gbulmer/openstm32hw/Orone-mini-v0/Orone-mini-S8J-v0r001/Orone-mini-S8J-v0r001.top.pdf

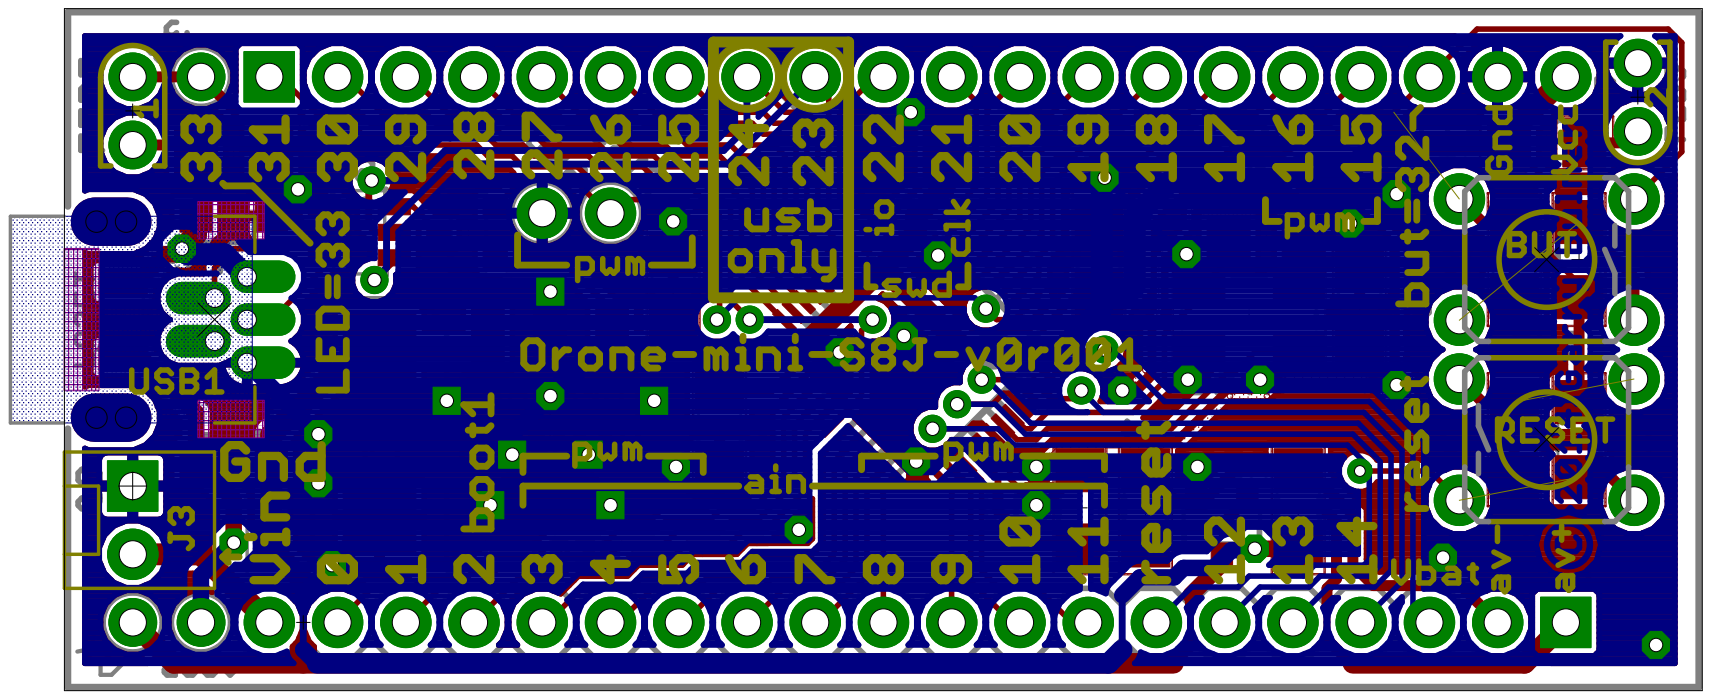
[picture p17: page 1]
