gbulmer/openstm32hw/Orone-mini-v0/Orone-mini-S8E-v0r001/Orone-mini-S8E-v0r001.pdf

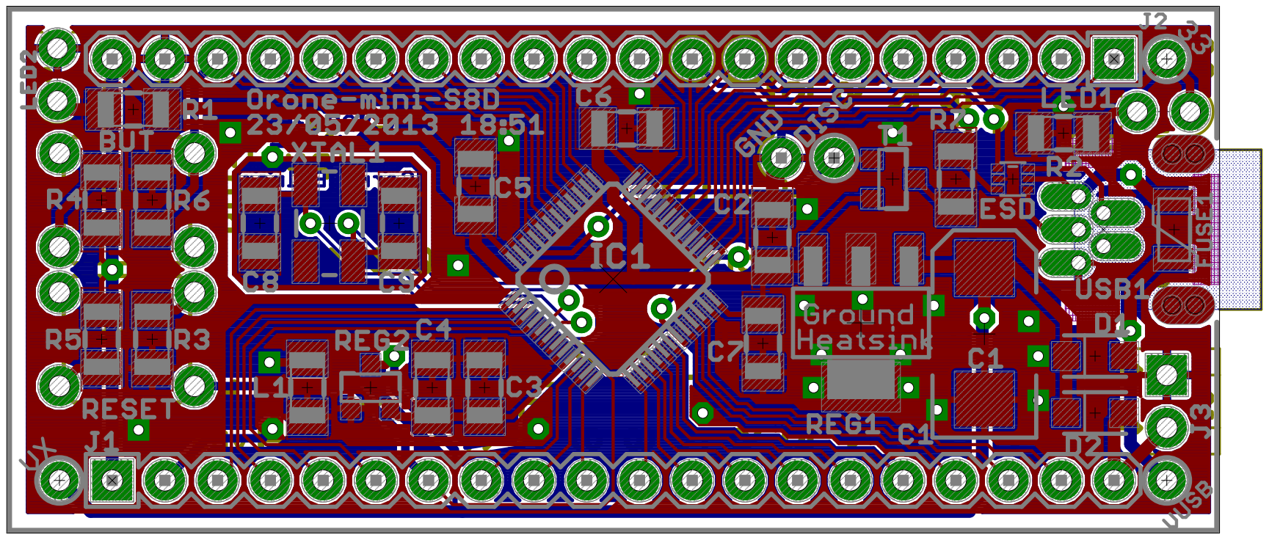
[picture p18: page 1]
