gbulmer/openstm32hw/Orone-mini-v0/Orone-mini-S8H-v0r001/Orone-mini-S8H-v0r001.pdf

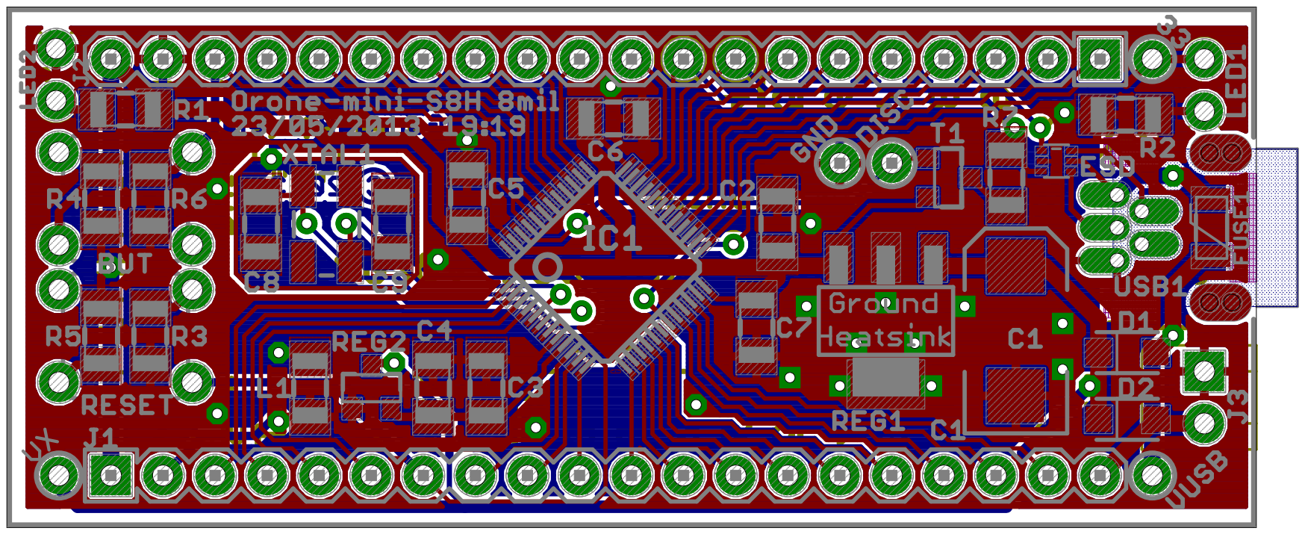
[picture p20: page 1]
