gbulmer/openstm32hw/Orone-mini-v0/Orone-mini-S8H-v0r001/Orone-mini-S8H-v0r001.top.pdf

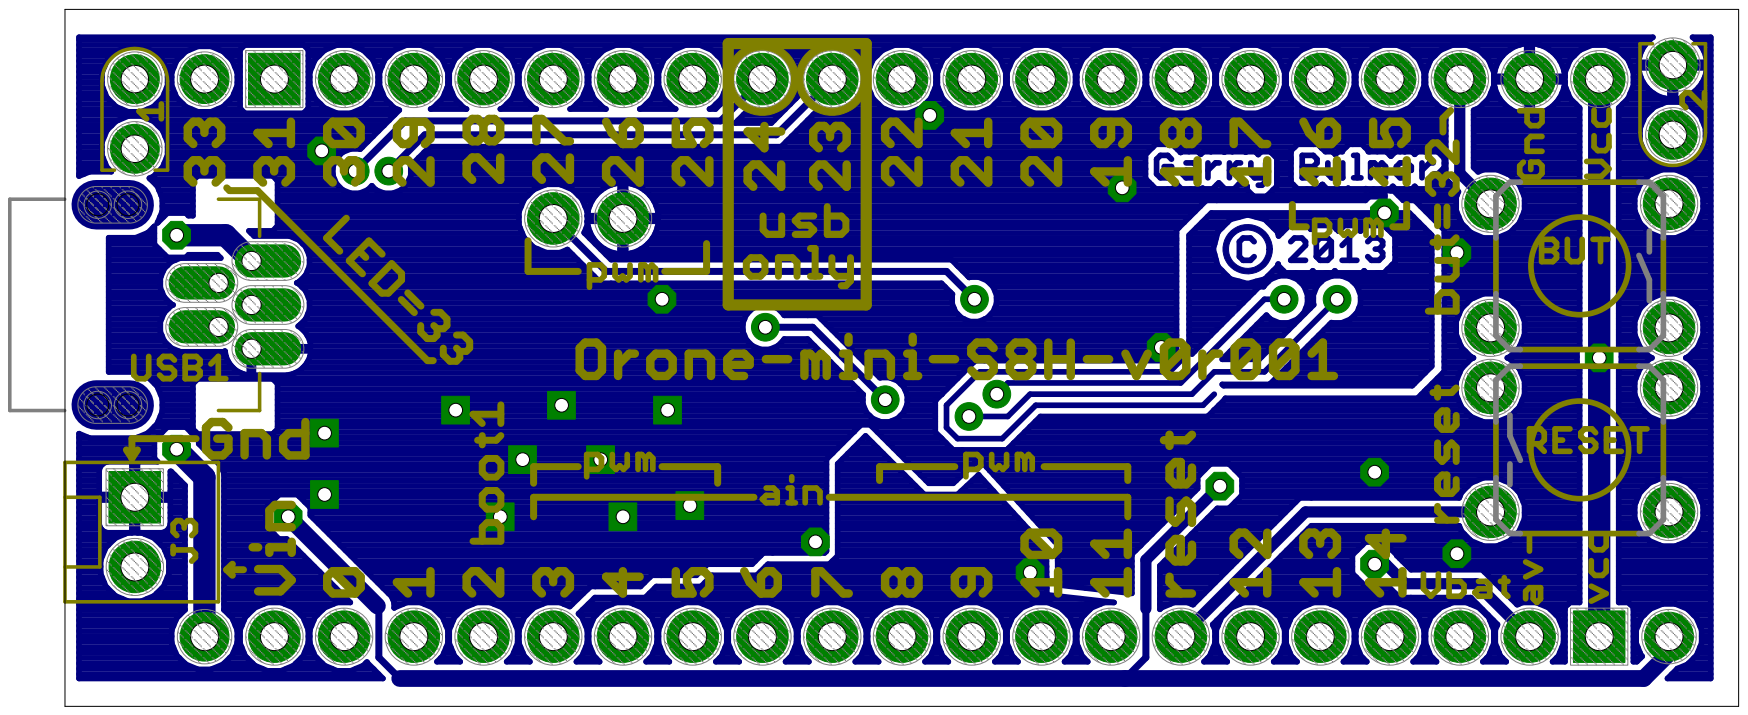
[picture p21: page 1]
