gbulmer/openstm32hw/Orone-mini-v0/Orone-mini-S8D-v0r001/Orone-mini-S8D-v0r001.sch.pdf

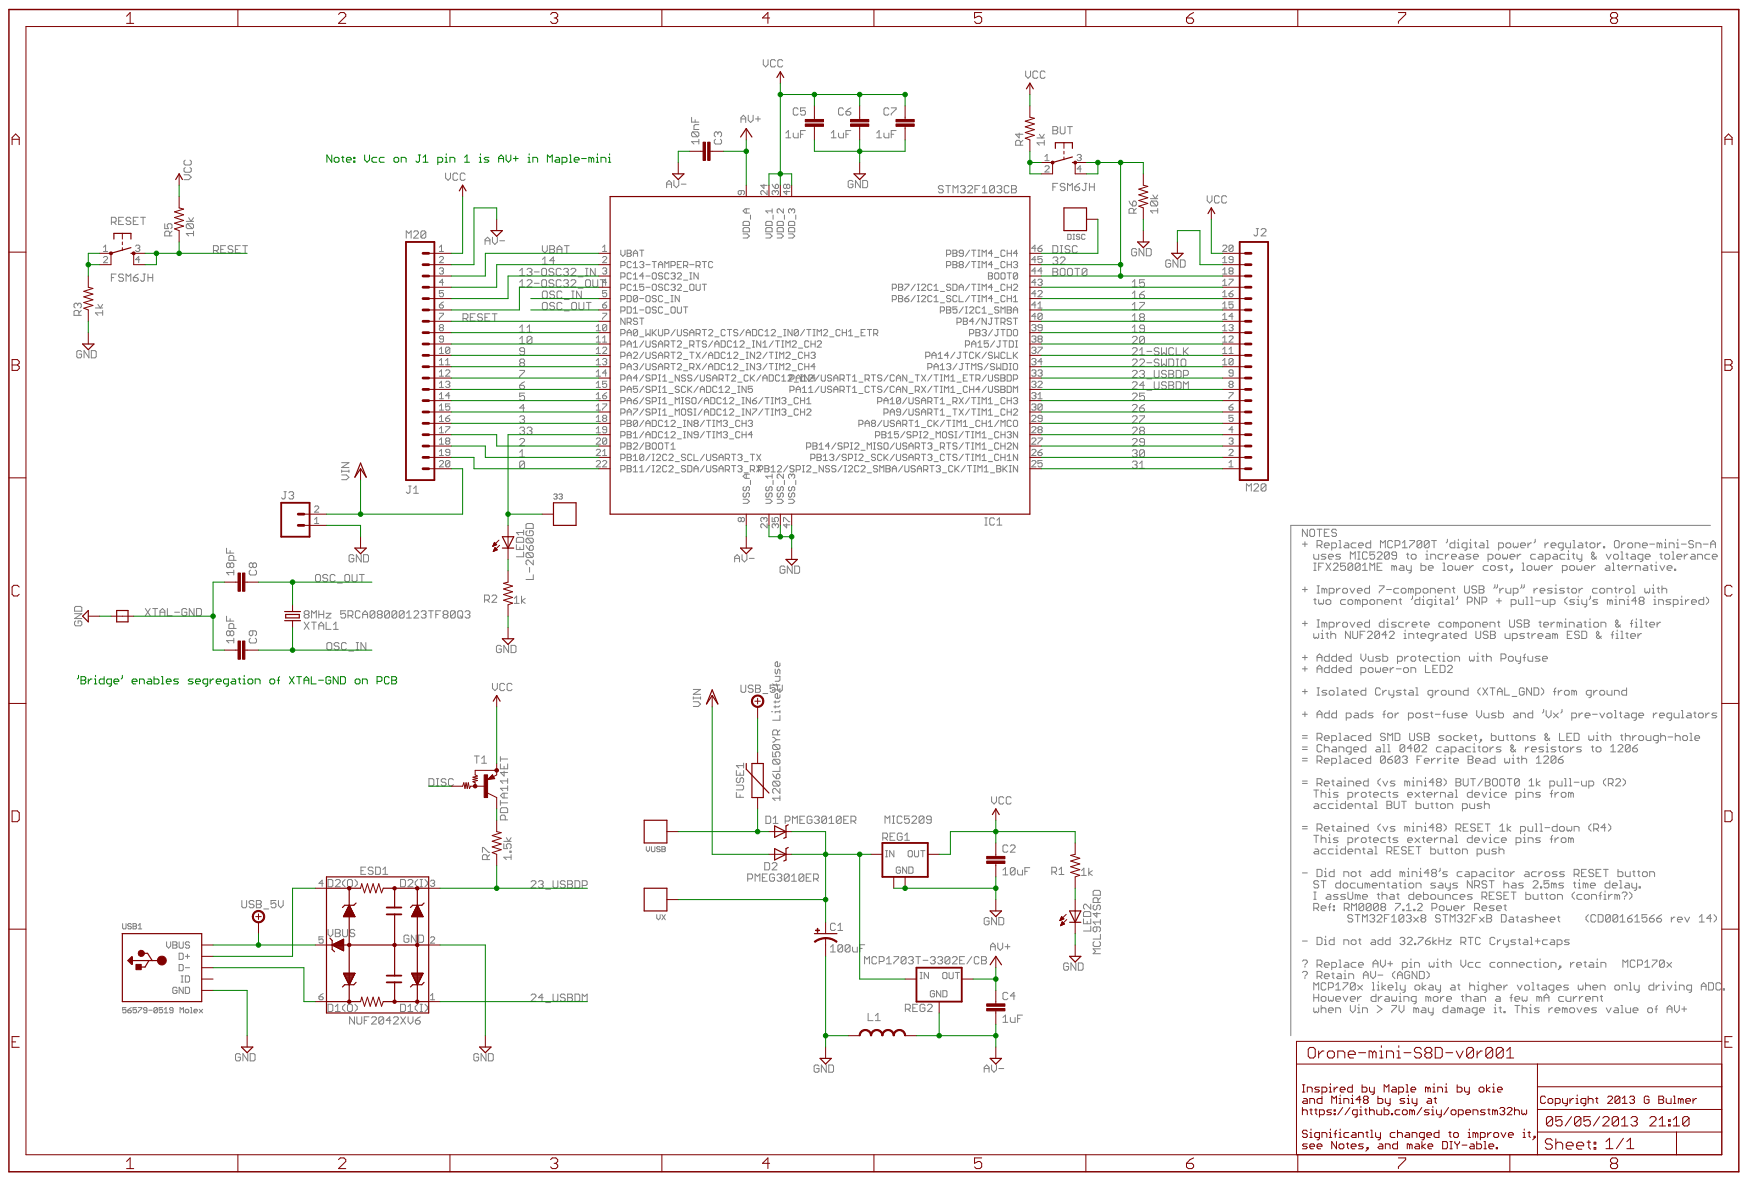
[picture p22: page 1]
