gbulmer/openstm32hw/Orone-mini-v0/Orone-mini-S8D-v0r001/Orone-mini-S8D-v0r001.pdf

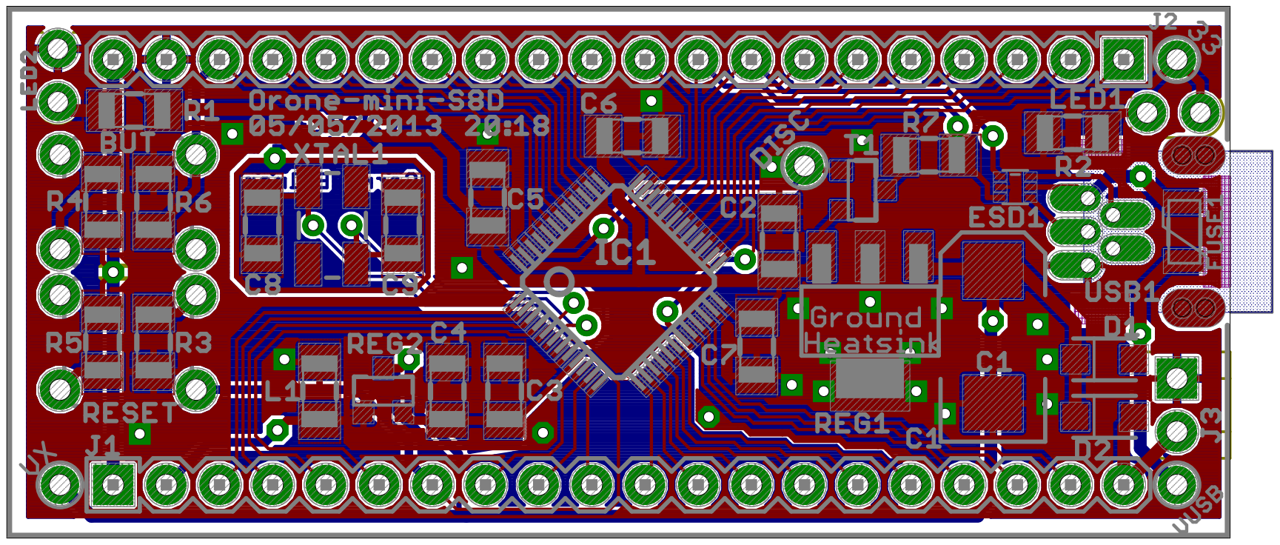
[picture p23: page 1]
