gbulmer/openstm32hw/Orone-mini-v0/Orone-mini-S8D-v0r001/Orone-mini-S8D-v0r001.top.pdf

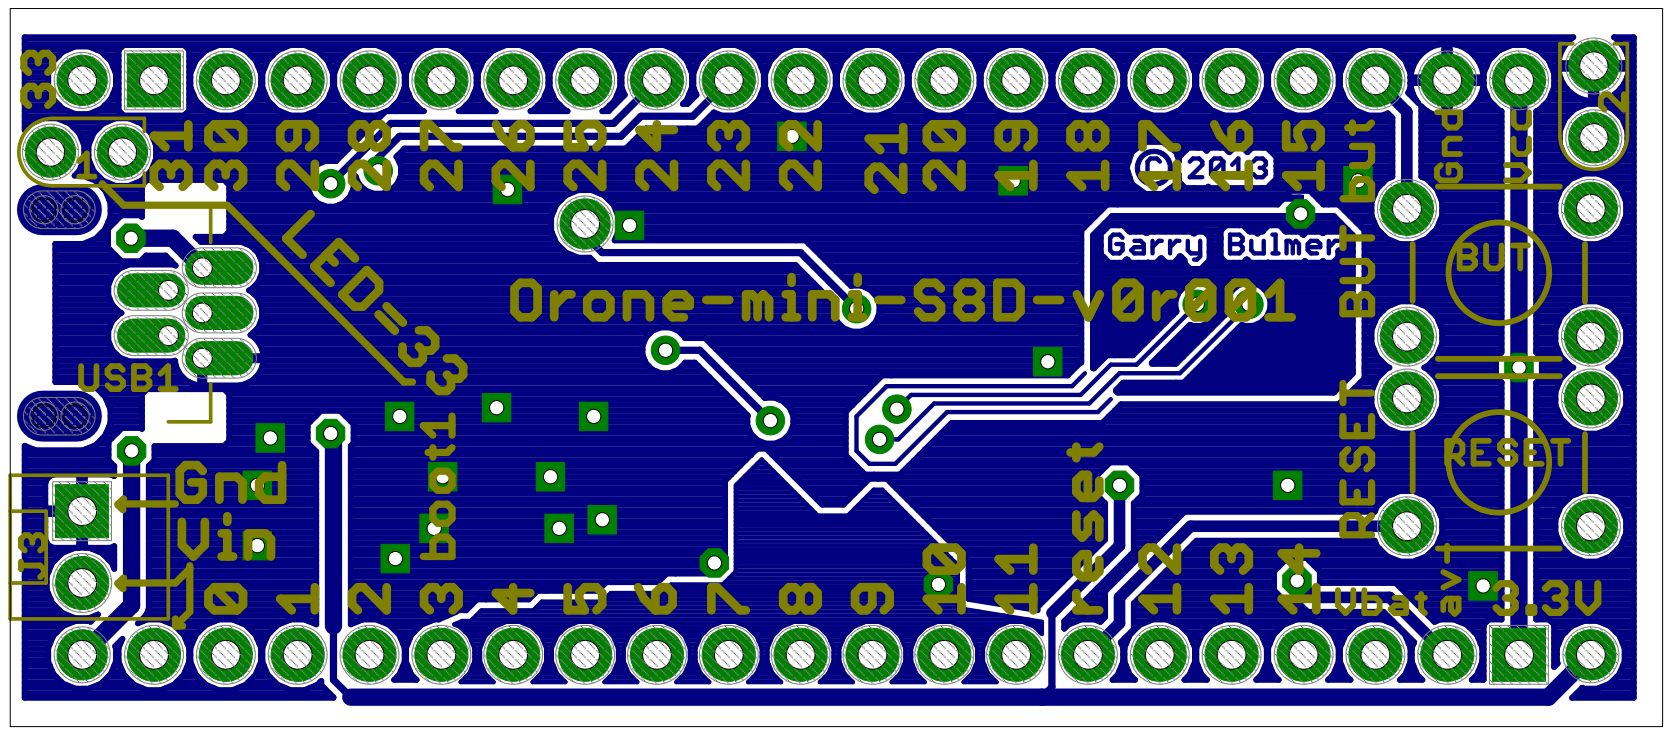
[picture p24: page 1]
