gbulmer/openstm32hw/Orone-mini-v0/Orone-mini-S8C-v0r001/Orone-mini-S8C-v0r001.pdf

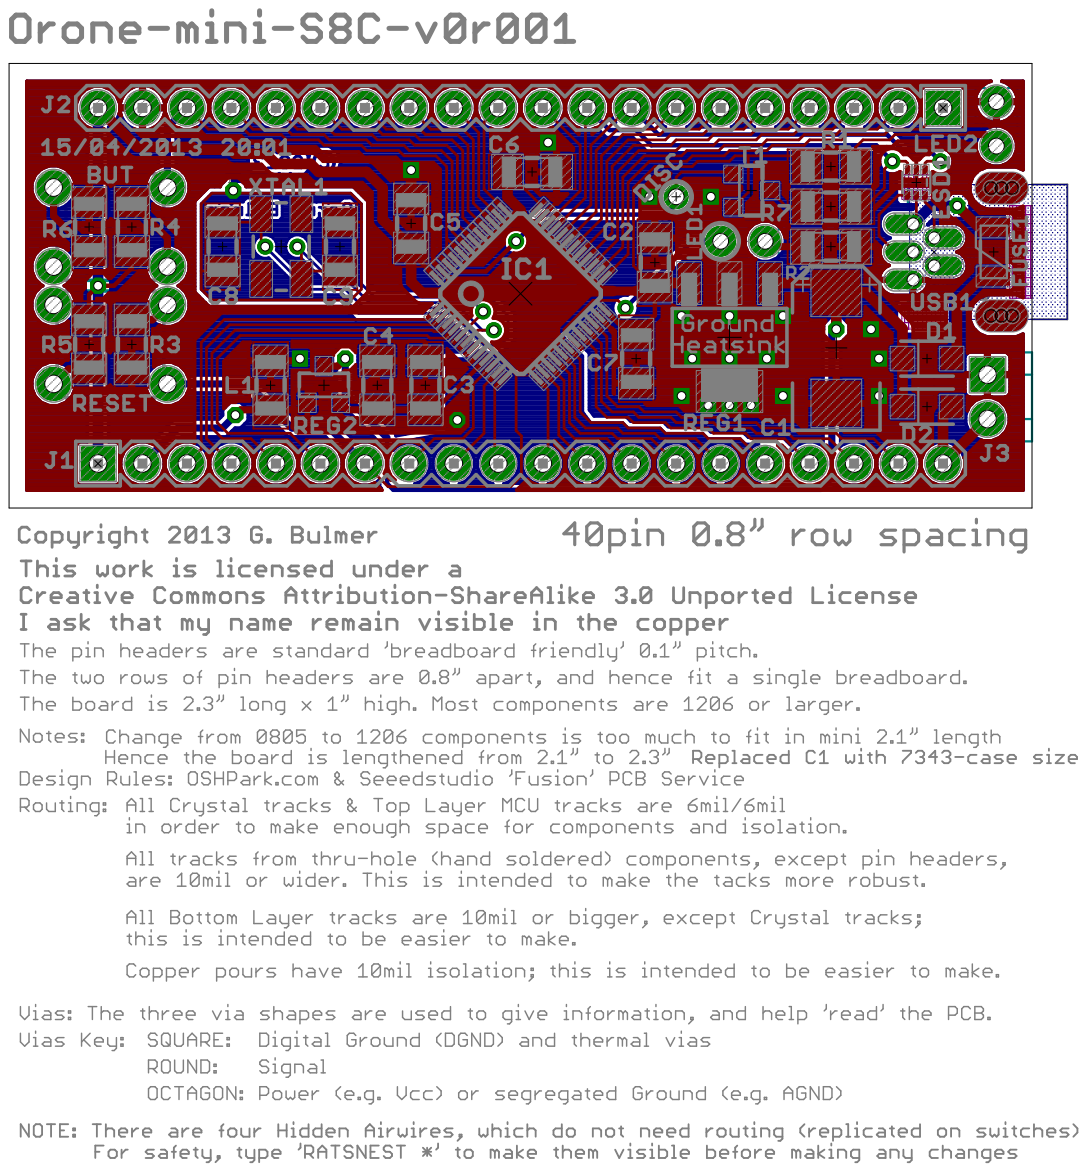
[picture p25: page 1]
