gbulmer/openstm32hw/Orone-mini-v0/Orone-mini-S8C-v0r001/Orone-mini-S8C-v0r001.sch.pdf

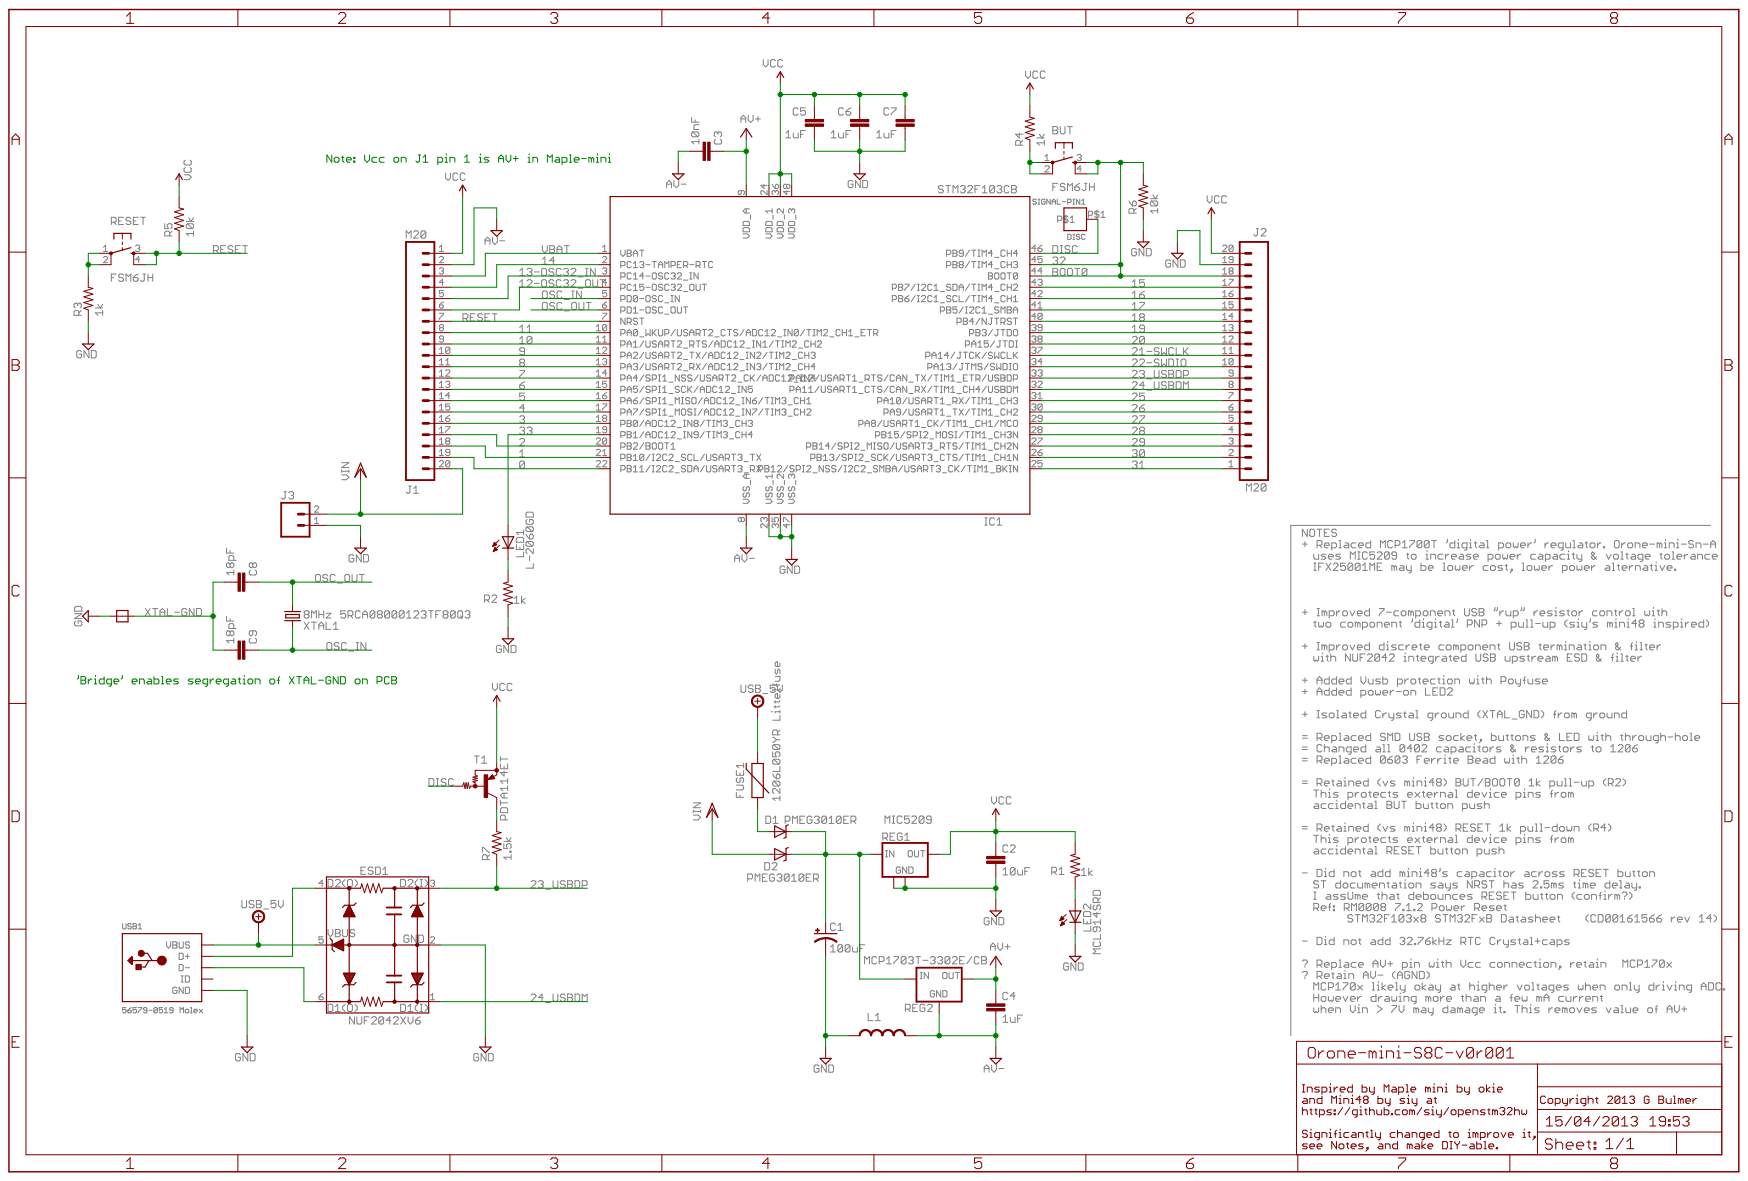
[picture p26: page 1]
