gbulmer/openstm32hw/Orone-mini-v0/Orone-mini-S8A-v0r001/Orone-mini-S8A-v0r001.pdf

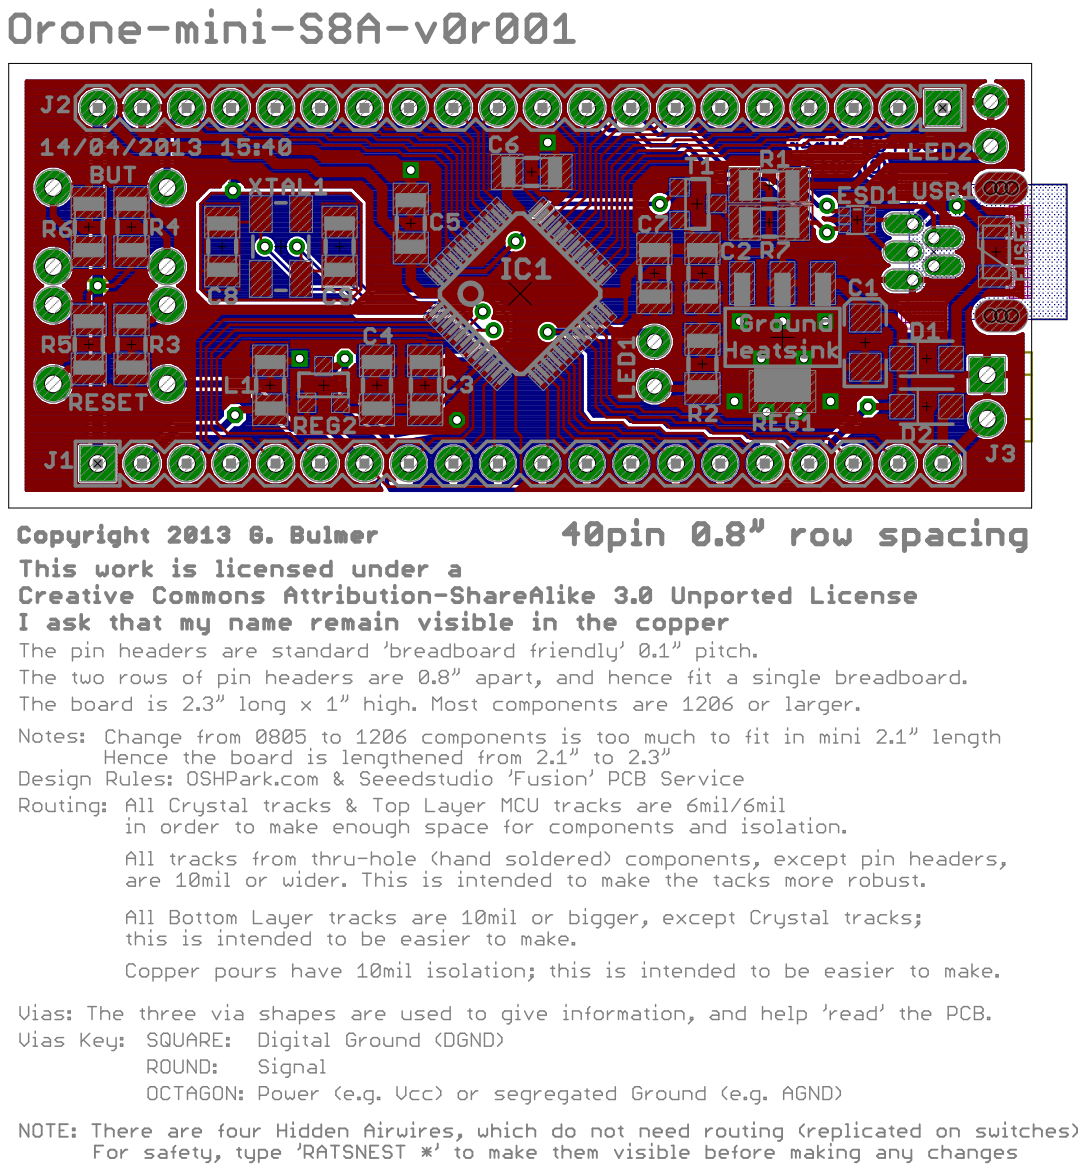
[picture p28: page 1]
