gbulmer/openstm32hw/Orone-mini-v0/Orone-mini-S8A-v0r001/Orone-mini-S8A-v0r001.sch.pdf

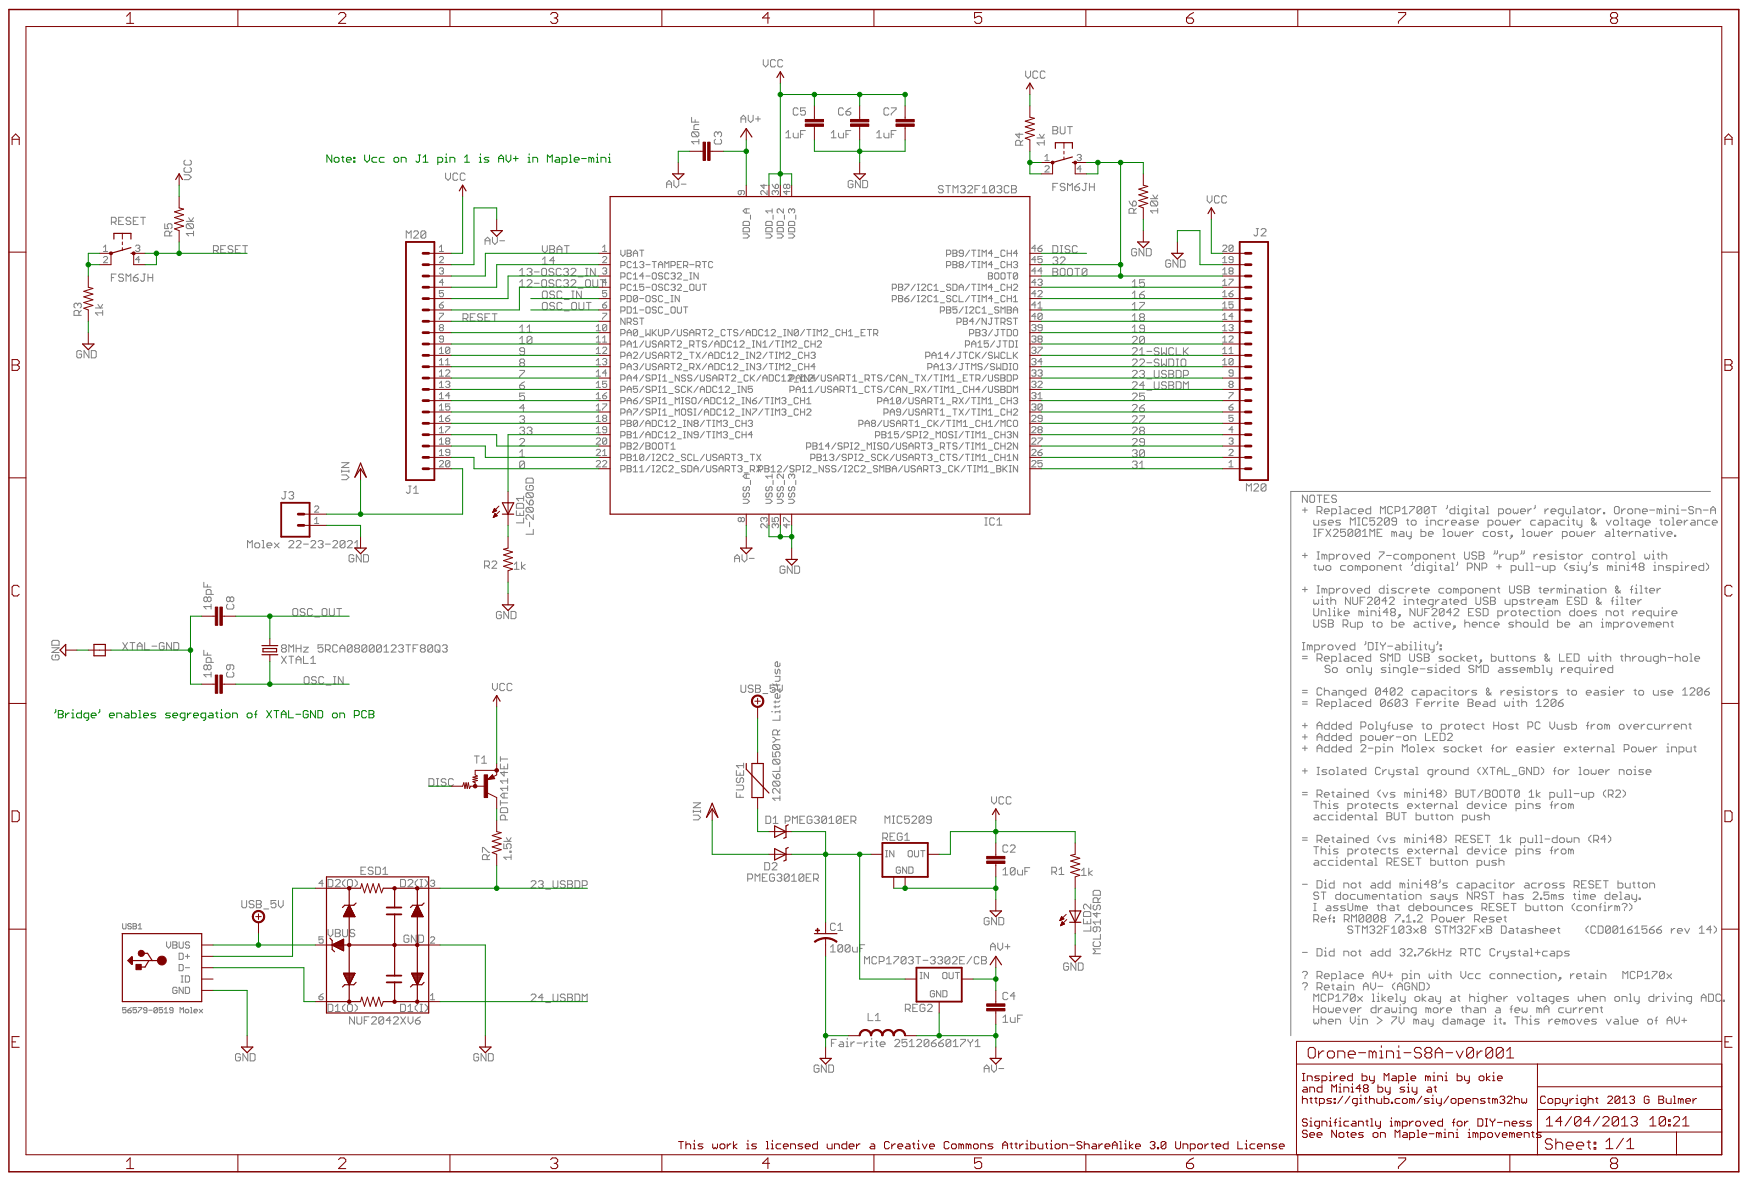
[picture p29: page 1]
