gbulmer/openstm32hw/Orone-mini-v0/Orone-mini-S8A-v0r001/Orone-mini-S8A-v0r001.top.pdf

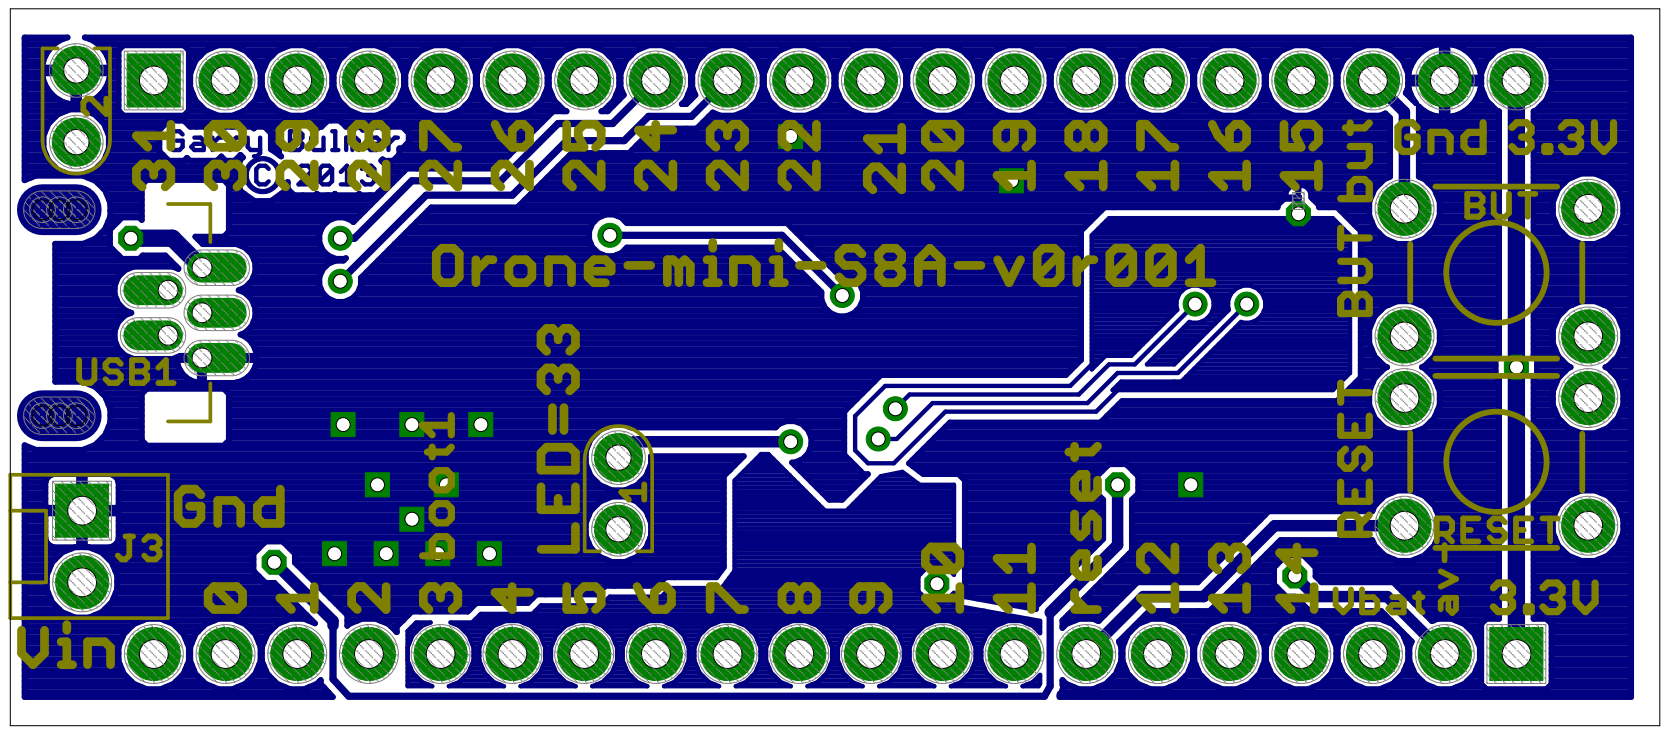
[picture p30: page 1]
