gbulmer/openstm32hw/mini48U/mini48U-v0.6.1-schematic.pdf

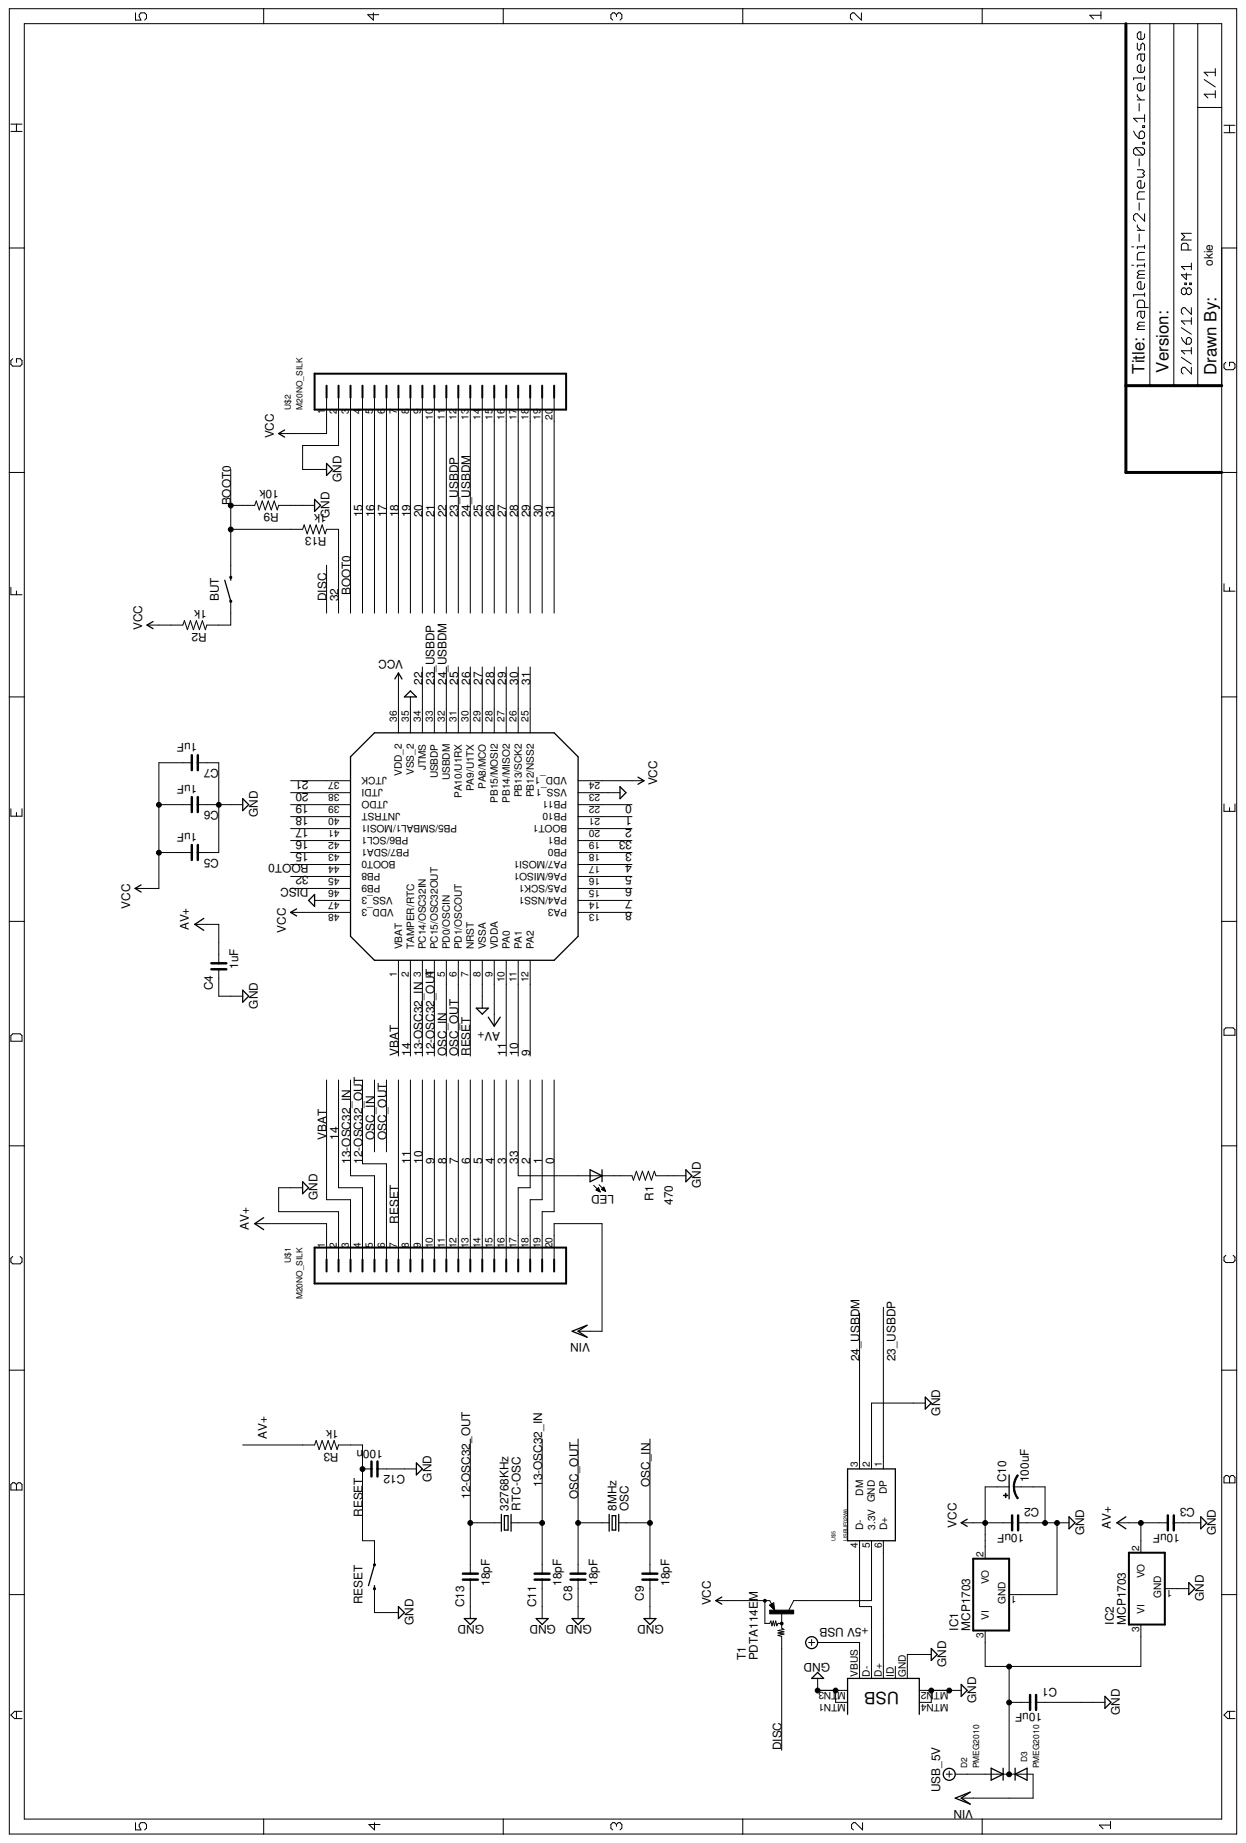
[picture p31: page 1]

470 VCC VCC VCC USB_5V Fu01 1uF Fu1 Fu1 Fu01 AV+ 18pF 18pF GND GND DNG DNG GND AV+ VCC GND AV+ GND k1 GNDk01 k1 NI V GND 8MHz NI V k1 n001 GND BSU V5+ VCC PDTA114EM GND GND GND DNG M20NO_SILK M20NO_SILK GND GND Fu01 GND 100uF 18pF 18pF DNG DNG 32768KHz CCV VCC VCC +VA GND PMEG2010 PMEG2010 MCP1703 MCP1703 Fu1 USBUF02W6 BOOT0 DEL R1 2 C C4 6 C5 C 3 C C9 C8 2 R 9 R 3 R OSC 31 R 21 C T1 D+D- VBUS GND ID 3 NT M 1 NT M 2 NT M 4 NT M BUT RESET 1234567891011121314151617181920 U$1 1234567891011121314151617181920U$2 1 C C10 C11 C13 RTC-OSC VBAT 1 TAMPER/RTC 2 PC14/OSC32IN 3 PC15/OSC32OUT 4 PD0/OSCIN 5 PD1/OSCOUT 6 NRST 7 VSSA 8 VDDA 9 PA0 10 PA1 11 PA2 12 3AP 31 1SSN/ 4AP 41 1KCS/ 5AP 51 1 OSI M/ 6AP 61 1I SOM/ 7AP 71 0BP 81 1BP 91 1T OOB 02 01BP 12 11BP 22 1_SSV 32 1_ DDV 42 PB12/NSS2 25 PB13/SCK2 26 PB14/MISO2 27 PB15/MOSI2 28 PA8/MCO 29 PA9/U1TX 30 PA10/U1RX 31 USBDM 32 USBDP 33 JTMS 34 VSS_2 35 VDD_2 36 KCTJ 73 I DTJ 83 ODTJ 93 TSRTNJ 04 1I SOM/ 1LAB MS/ 5BP 14 1L CS/ 6BP 24 1ADS/ 7BP 34 0T OOB 44 8BP 54 9BP 64 3_SSV 74 3_ DDV 84 D2D3 VI 3 1 VO 2 IC1 GND VI 3 1 VO 2 IC2 GND 7 C DP 1 GND 2 DM 3 D- 4 3.3V 5 D+ 6 U$5 DISC CSI D DISC AV+ OSC_IN OSC_IN OSC_IN OSC_OUT OSC_OUT OSC_OUT RESET RESET RESET VBAT VBAT 23_USBDP 23_USBDP 23_USBDP 33 33 0 0 1 1 2 2 3 3 4 4 5 5 6 6 7 7 8 8 9 9 10 10 11 11 12-OSC32_OUT 12-OSC32_OUT 12-OSC32_OUT 13-OSC32_IN 13-OSC32_IN 13-OSC32_IN 14 14 15 51 16 61 17 71 18 81 19 91 20 02 21 12 22 22 24_USBDM 24_USBDM 24_USBDM 25 25 26 26 27 27 28 28 29 29 30 30 31 31 32 23 BOOT0 0T OOB okie Drawn By: Title: Version: BSU
